fitzterra/battery-capacity-meter/doc/Firmware/Screen_Design/OLED128x64_Disharge_Complete.png

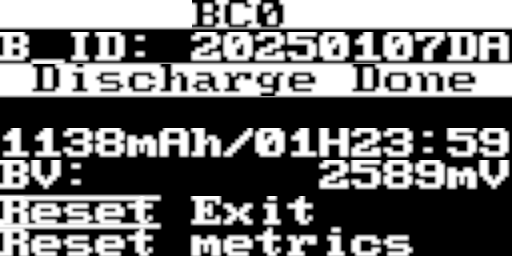
doc/Firmware/Screen_Design/OLED128x64_Disharge_Complete.png
