fitzterra/battery-capacity-meter/Firmware/src/testing/mqtt.py

"""
Test module for MQTT.

Basically from here:
    https://github.com/peterhinch/micropython-mqtt/blob/master/README.md#23-example-usage
"""

import asyncio
from lib.mqtt_as import MQTTClient, config

# Local configuration
config["ssid"] = "GaulNetIoT"
config["wifi_pw"] = "G4u7N3t10T"
config["server"] = "mqttix.gaul.za"


async def messages(client):  # Respond to incoming messages
    # If MQTT V5is used this would read
    # async for topic, msg, retained, properties in client.queue:
    async for topic, msg, retained in client.queue:
        print(topic.decode(), msg.decode(), retained)


async def up(client):  # Respond to connectivity being (re)established
    while True:
        await client.up.wait()  # Wait on an Event
        client.up.clear()
        await client.subscribe("foo_topic", 1)  # renew subscriptions


async def main(client):
    await client.connect()
    for coroutine in (up, messages):
        asyncio.create_task(coroutine(client))
    n = 0
    while True:
        await asyncio.sleep(5)
        print("publish", n)
        # If WiFi is down the following will pause for the duration.
        await client.publish("result", "{}".format(n), qos=1)
        n += 1


config["queue_len"] = 1  # Use event interface with default queue size
MQTTClient.DEBUG = True  # Optional: print diagnostic messages
client = MQTTClient(config)
try:
    asyncio.run(main(client))
finally:
    client.close()  # Prevent LmacRxBlk:1 errors
